mattpidden/bike-navigation/firmware/libaries/TFT_eSPI_Setups/Setup207_GC9A01.h

#define USER_SETUP_ID 207
#define USER_SETUP_INFO "ESP32-S3-Touch-LCD-1.28"

#ifdef ILI9341_DRIVER
#undef ILI9341_DRIVER
#endif

#define GC9A01_DRIVER

// For ESP32 Dev board (only tested with GC9A01 display)
// The hardware SPI can be mapped to any pins

#define TFT_WIDTH  240
#define TFT_HEIGHT 240

#define TFT_MISO -1
#define TFT_MOSI 11
#define TFT_SCLK 10
#define TFT_CS   9  // Chip select control pin
#define TFT_DC   8  // Data Command control pin
#define TFT_RST  12
#define TFT_BL	40
#define TFT_BACKLIGHT_ON HIGH

#define LOAD_GLCD   // Font 1. Original Adafruit 8 pixel font needs ~1820 bytes in FLASH
#define LOAD_FONT2  // Font 2. Small 16 pixel high font, needs ~3534 bytes in FLASH, 96 characters
#define LOAD_FONT4  // Font 4. Medium 26 pixel high font, needs ~5848 bytes in FLASH, 96 characters
#define LOAD_FONT6  // Font 6. Large 48 pixel font, needs ~2666 bytes in FLASH, only characters 1234567890:-.apm
#define LOAD_FONT7  // Font 7. 7 segment 48 pixel font, needs ~2438 bytes in FLASH, only characters 1234567890:.
#define LOAD_FONT8  // Font 8. Large 75 pixel font needs ~3256 bytes in FLASH, only characters 1234567890:-.
#define LOAD_GFXFF  // FreeFonts. Include access to the 48 Adafruit_GFX free fonts FF1 to FF48 and custom fonts

#define SMOOTH_FONT

#define SPI_FREQUENCY  80000000
#define USE_HSPI_PORT
